jaaronkot/cherish-75/imgs/mcu.png

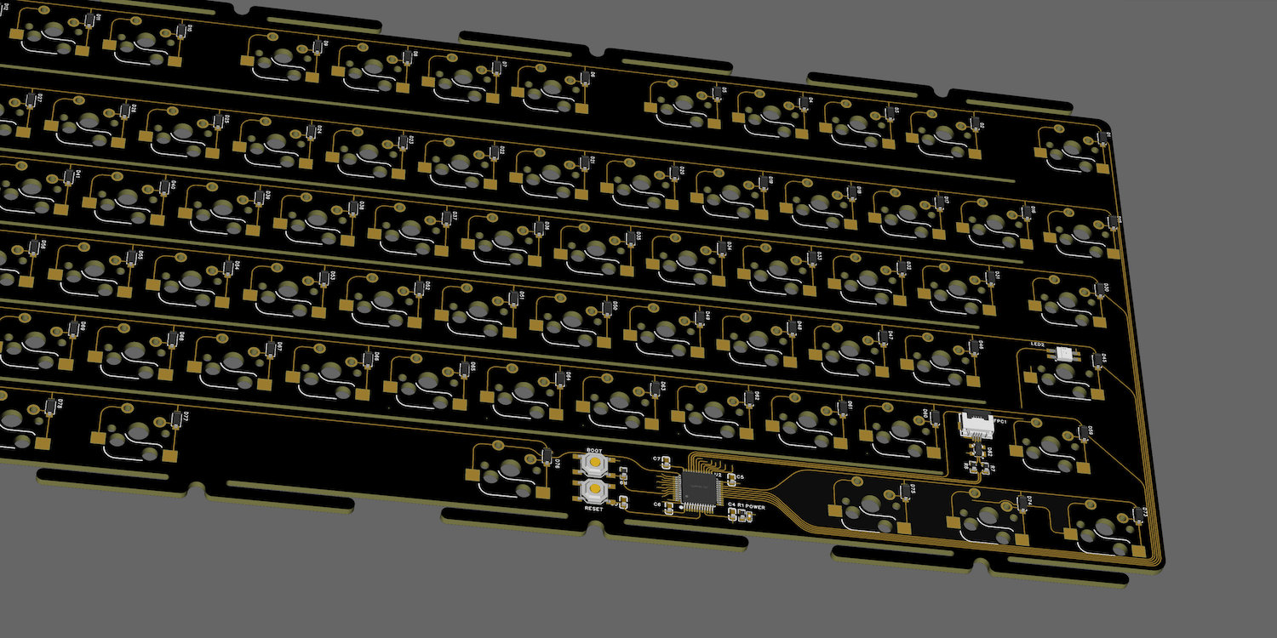
imgs/mcu.png
