jaaronkot/cherish-75/imgs/pcb-2.jpg

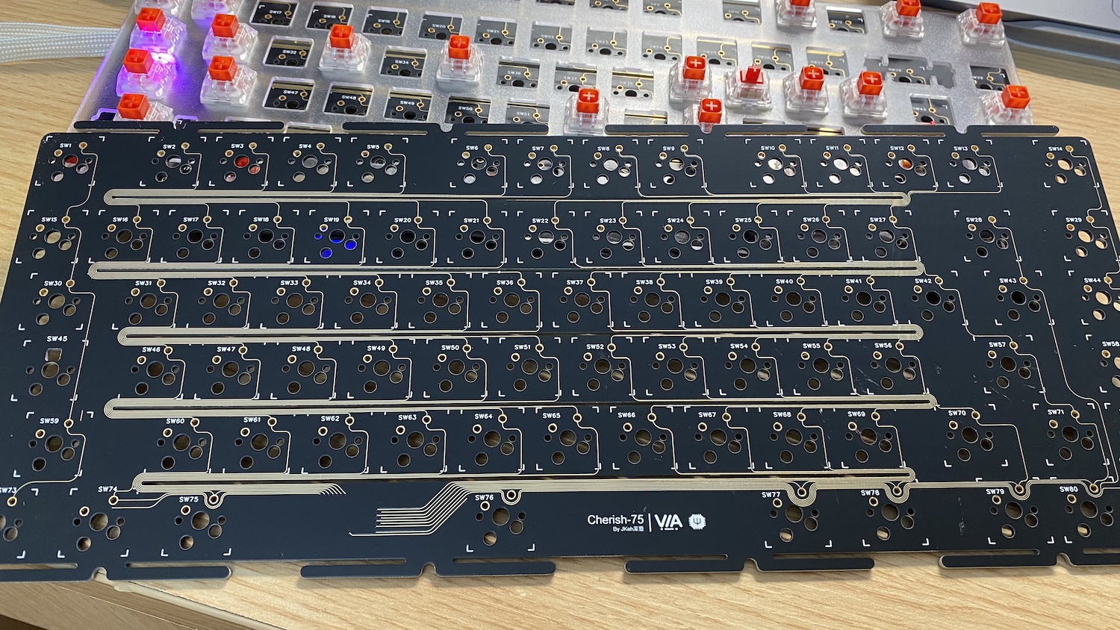
imgs/pcb-2.jpg
