jaaronkot/cherish-75/imgs/plate-1.jpg

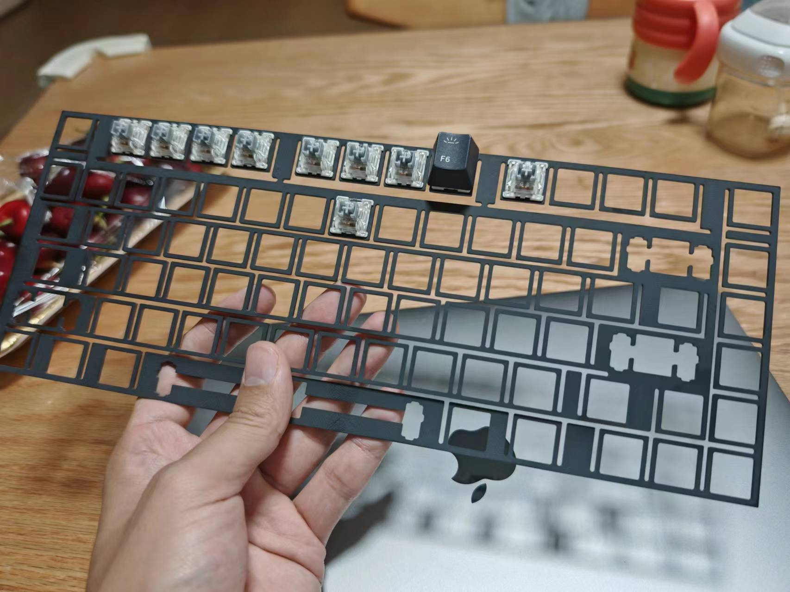
imgs/plate-1.jpg
